TheUncleKai/bbsensor/hardware/RTD/plot/RTD-F_Mask.pdf

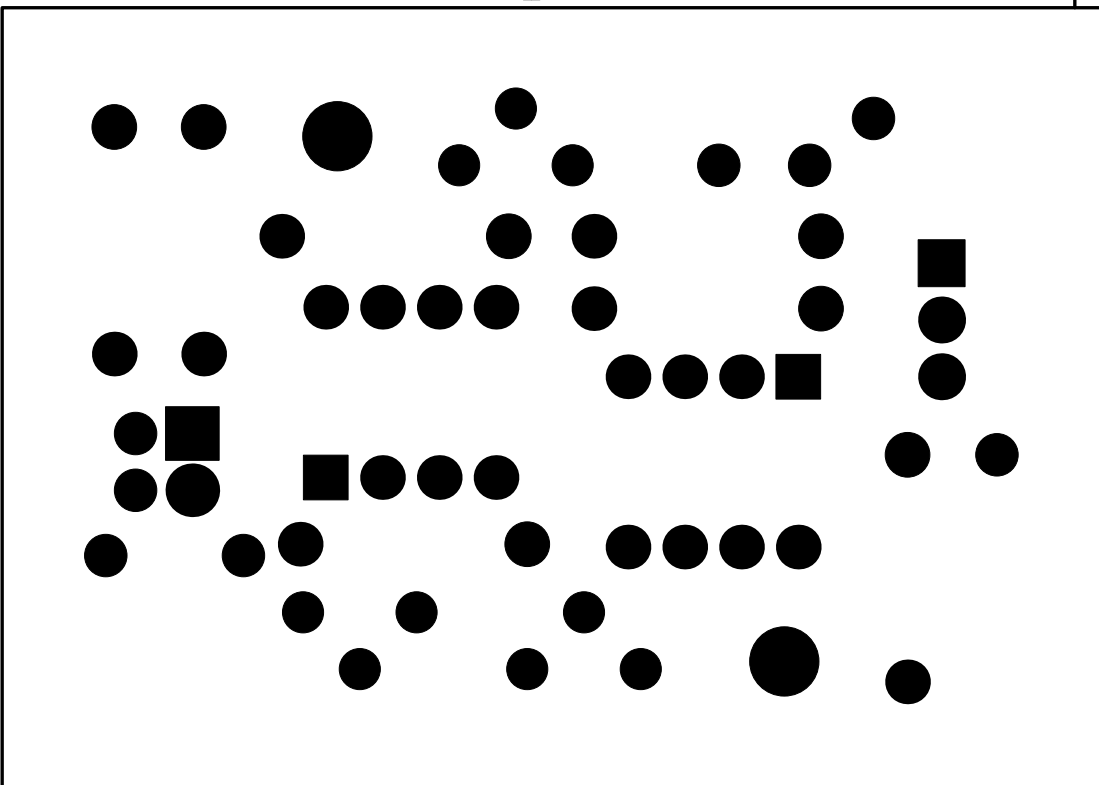
[picture p13: page 1]

File: RTD.kicad_pcb Sheet: Amplifier for Pt100 sensors
