TheUncleKai/bbsensor/hardware/RTD/plot/RTD-F_SilkS.pdf

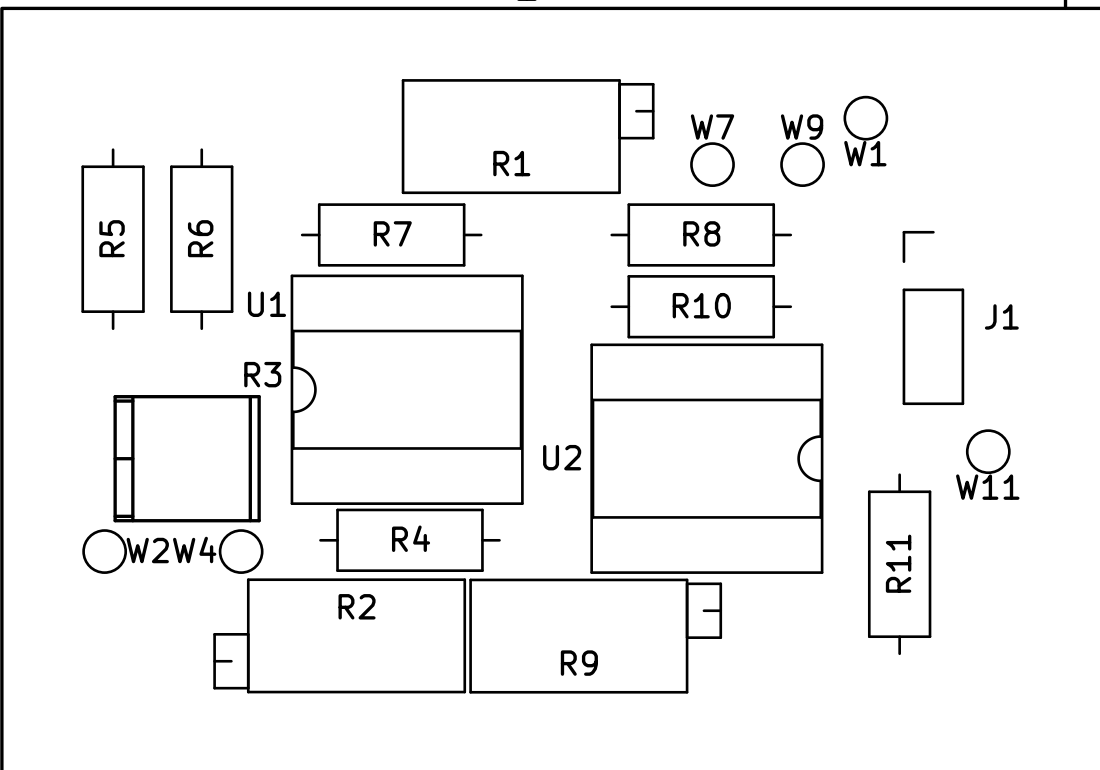
[picture p14: page 1]

File: RTD.kicad_pcb Sheet: Amplifier for Pt100 sensors
