TheUncleKai/bbsensor/hardware/Sensor/plot/BBSensor-B_Cu.pdf

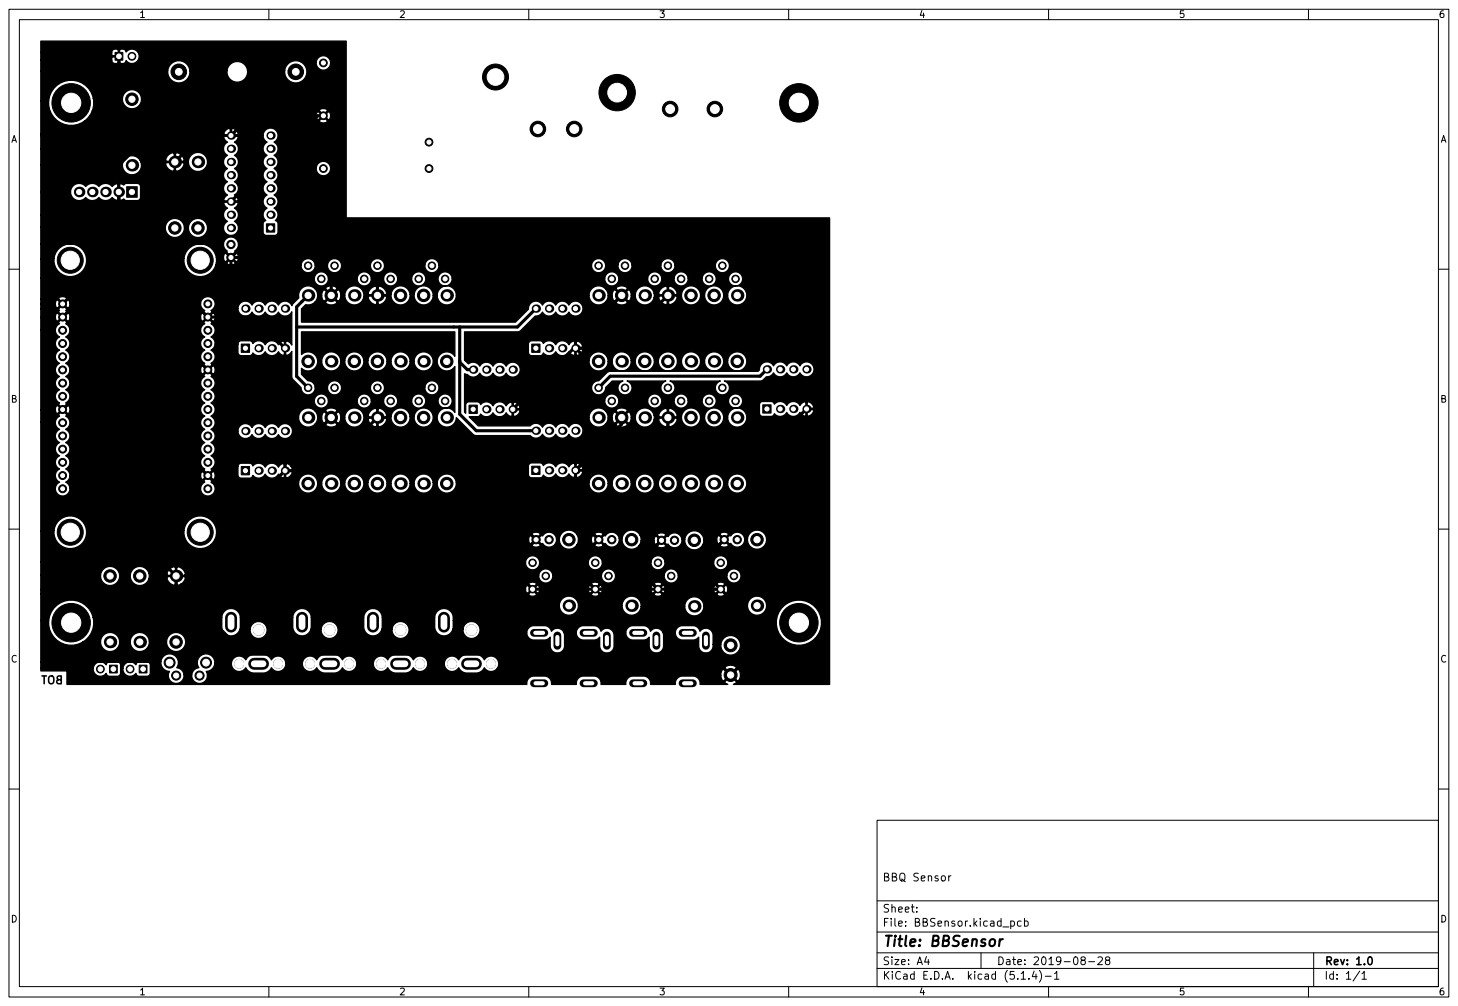
[picture p15: page 1]

File: BBSensor.kicad_pcb Sheet: BBQ Sensor BOT
