TheUncleKai/bbsensor/hardware/Sensor/plot/BBSensor-Edge_Cuts.pdf

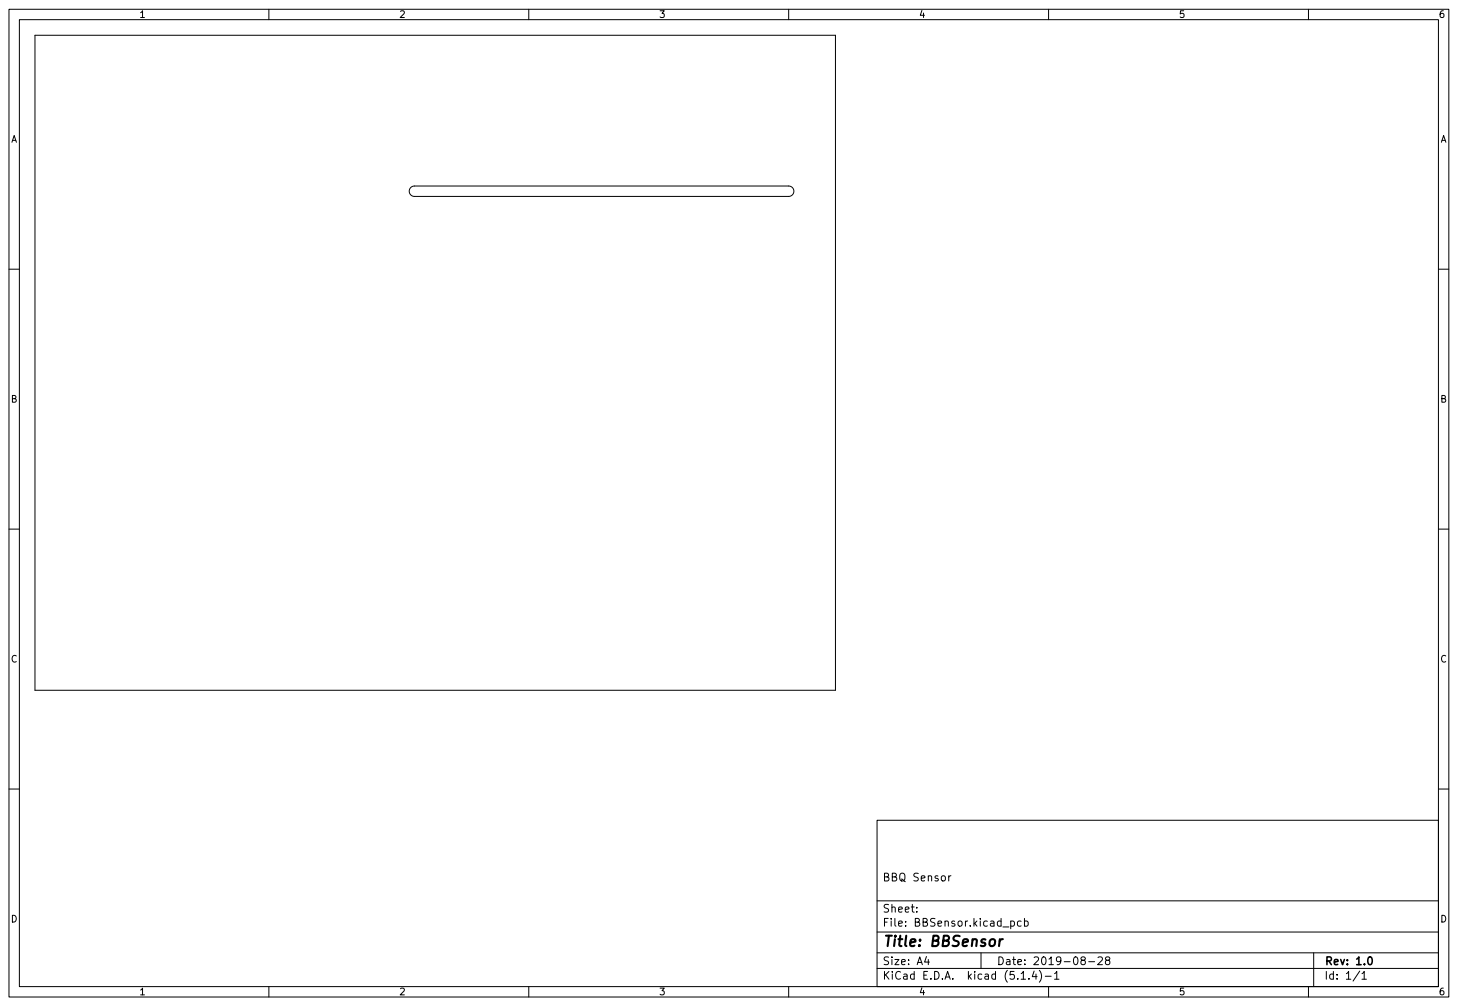
[picture p16: page 1]

File: BBSensor.kicad_pcb Sheet: BBQ Sensor
