TheUncleKai/bbsensor/hardware/Sensor/plot/BBSensor-F_Cu.pdf

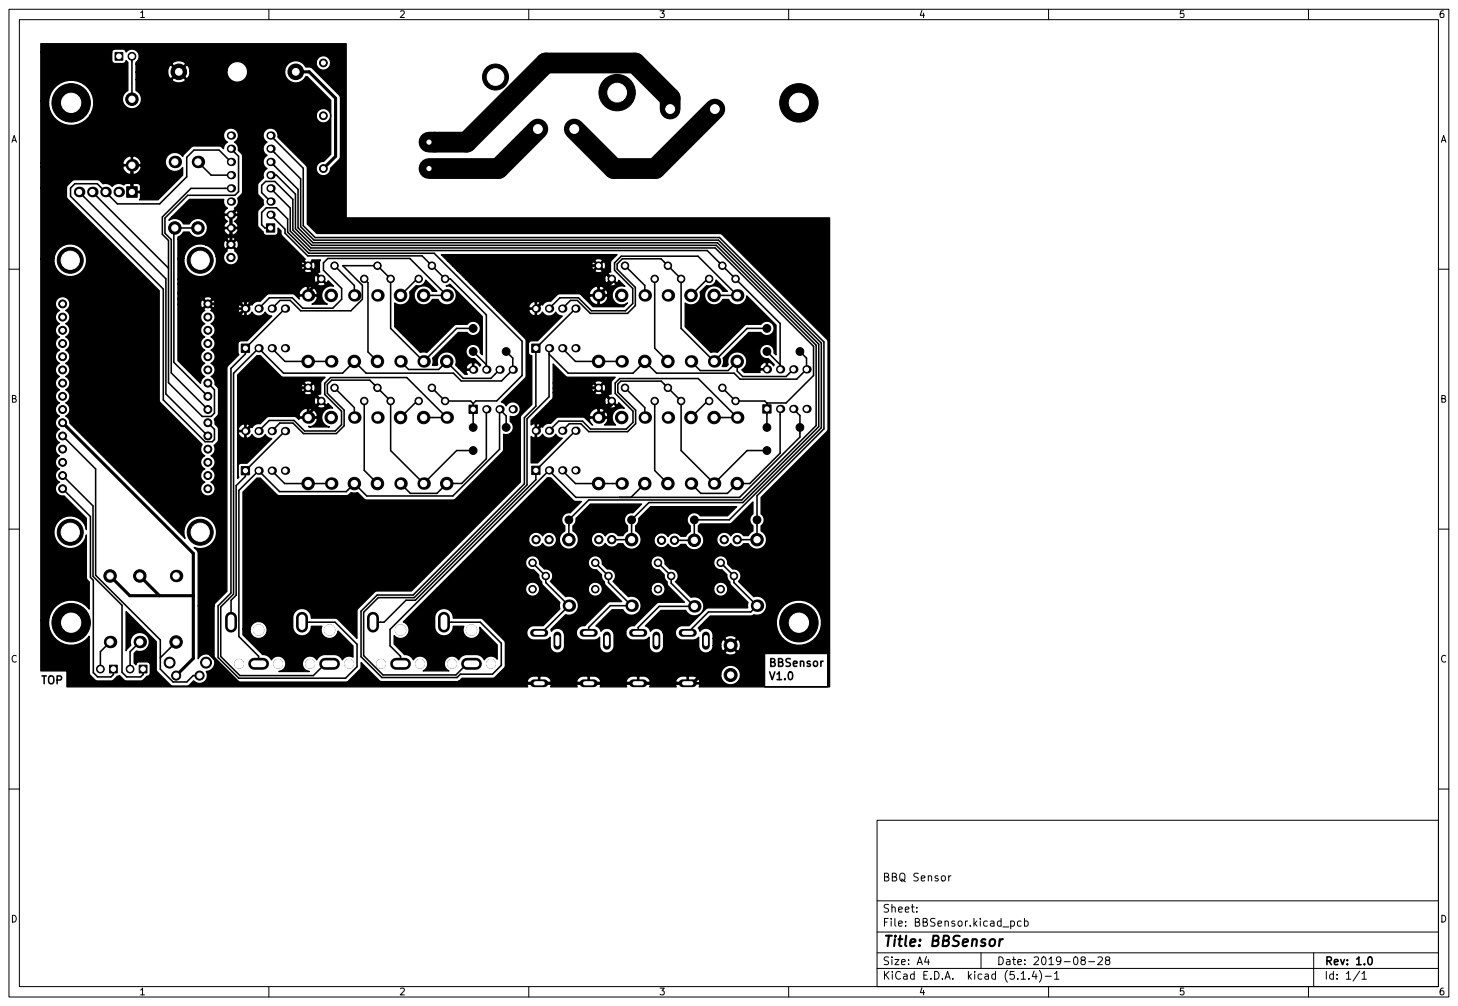
[picture p17: page 1]

File: BBSensor.kicad_pcb Sheet: BBQ Sensor BBSensor V1.0 TOP
