TheUncleKai/bbsensor/doc/pt100.pdf

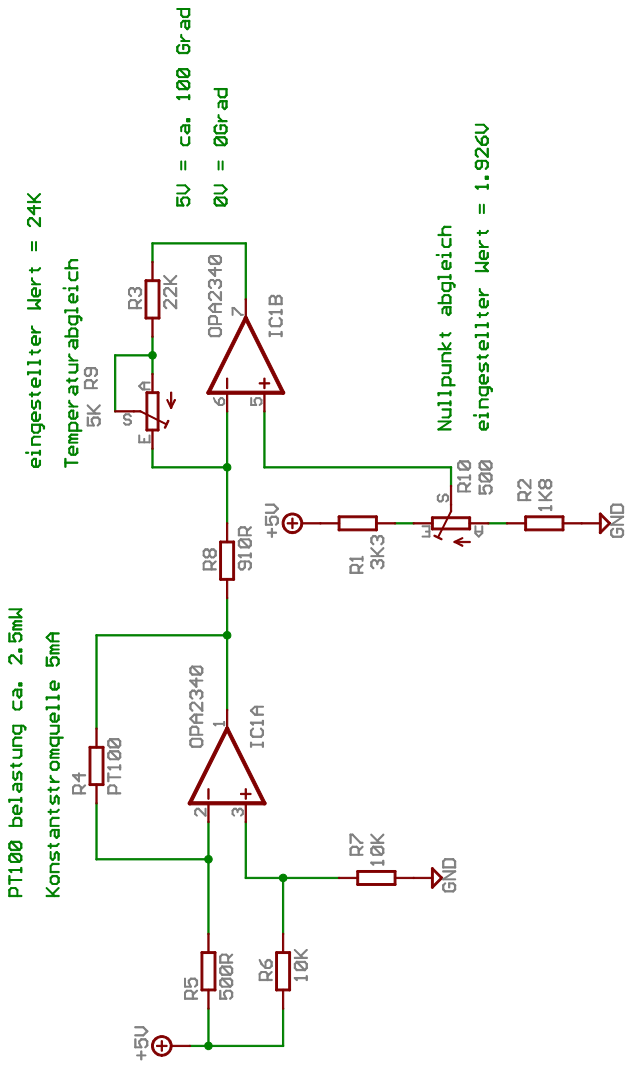
[picture p23: page 1]
