TheUncleKai/bbsensor/doc/pt100_2.pdf

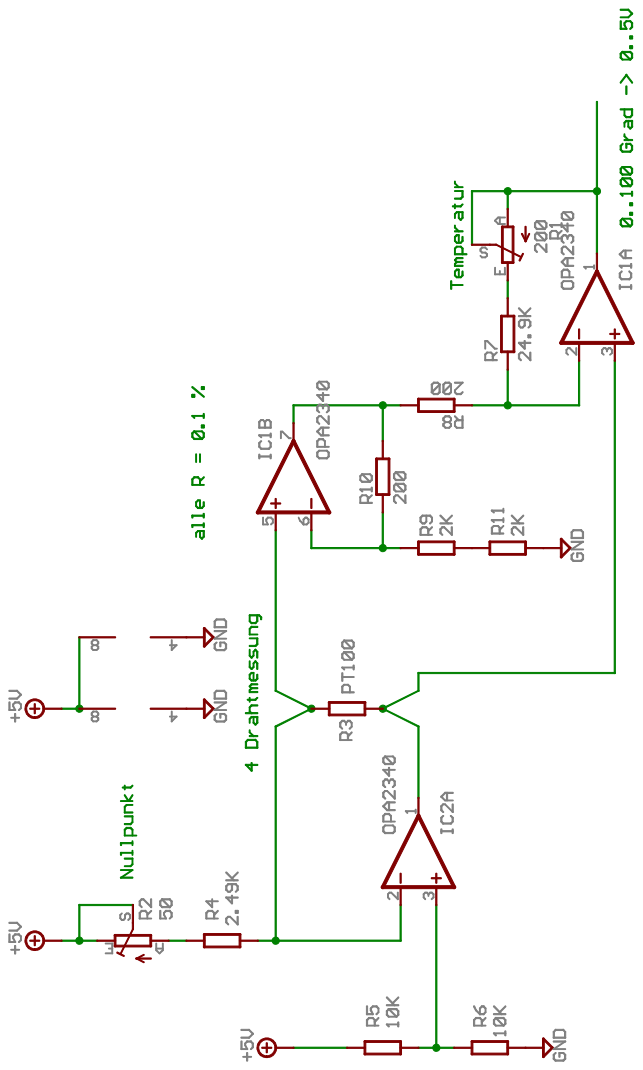
[picture p24: page 1]
