TheUncleKai/bbsensor/doc/pt100_3.pdf

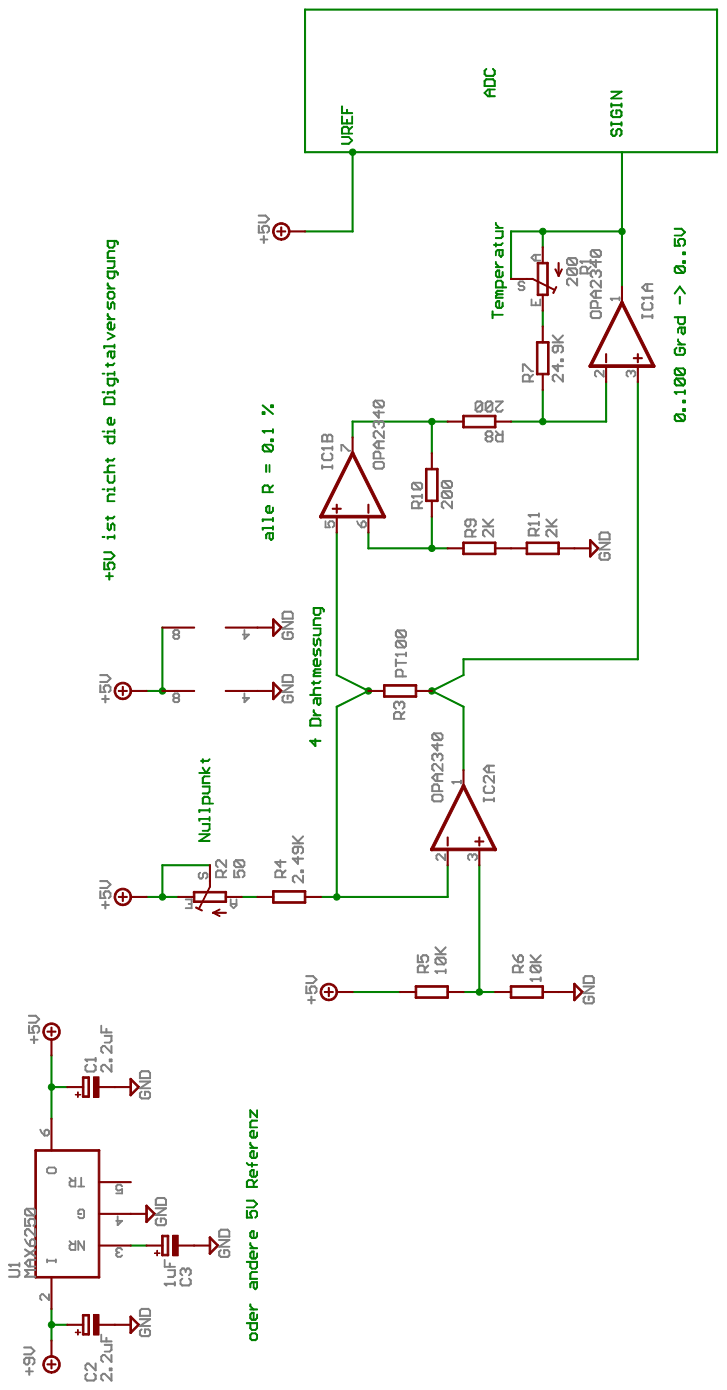
[picture p25: page 1]
