TheUncleKai/bbsensor/doc/pt100_4.pdf

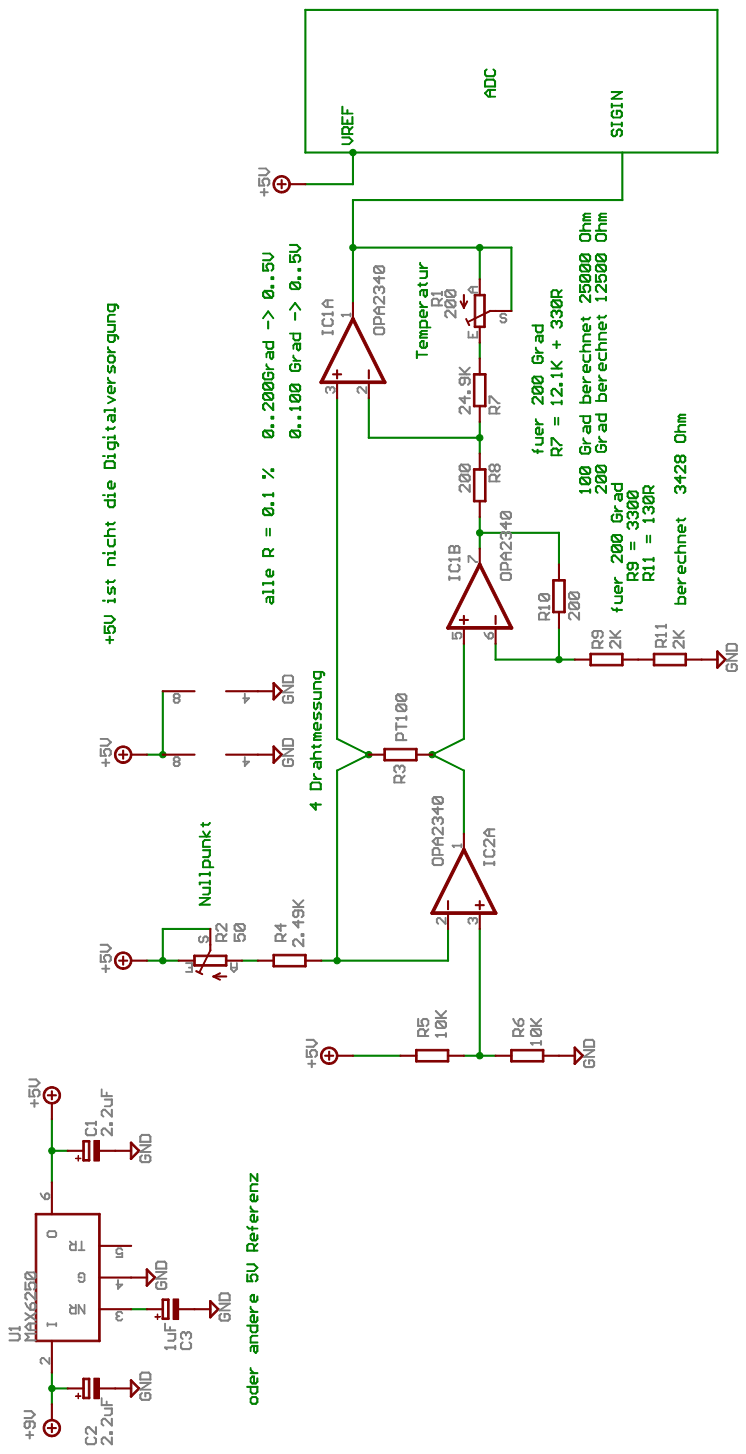
[picture p26: page 1]
