TheUncleKai/bbsensor/doc/pt100_5.pdf

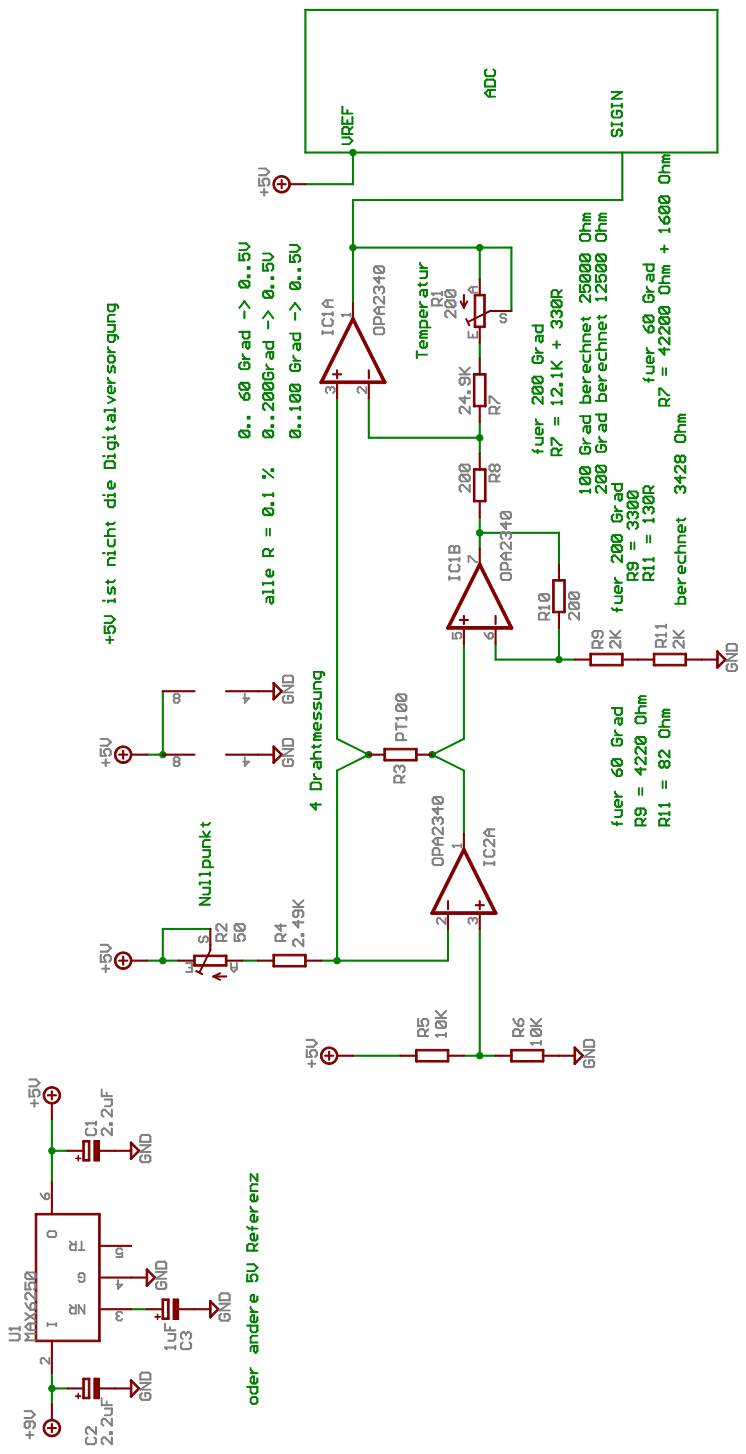
[picture p27: page 1]
