TheUncleKai/bbsensor/doc/pt100_6.pdf

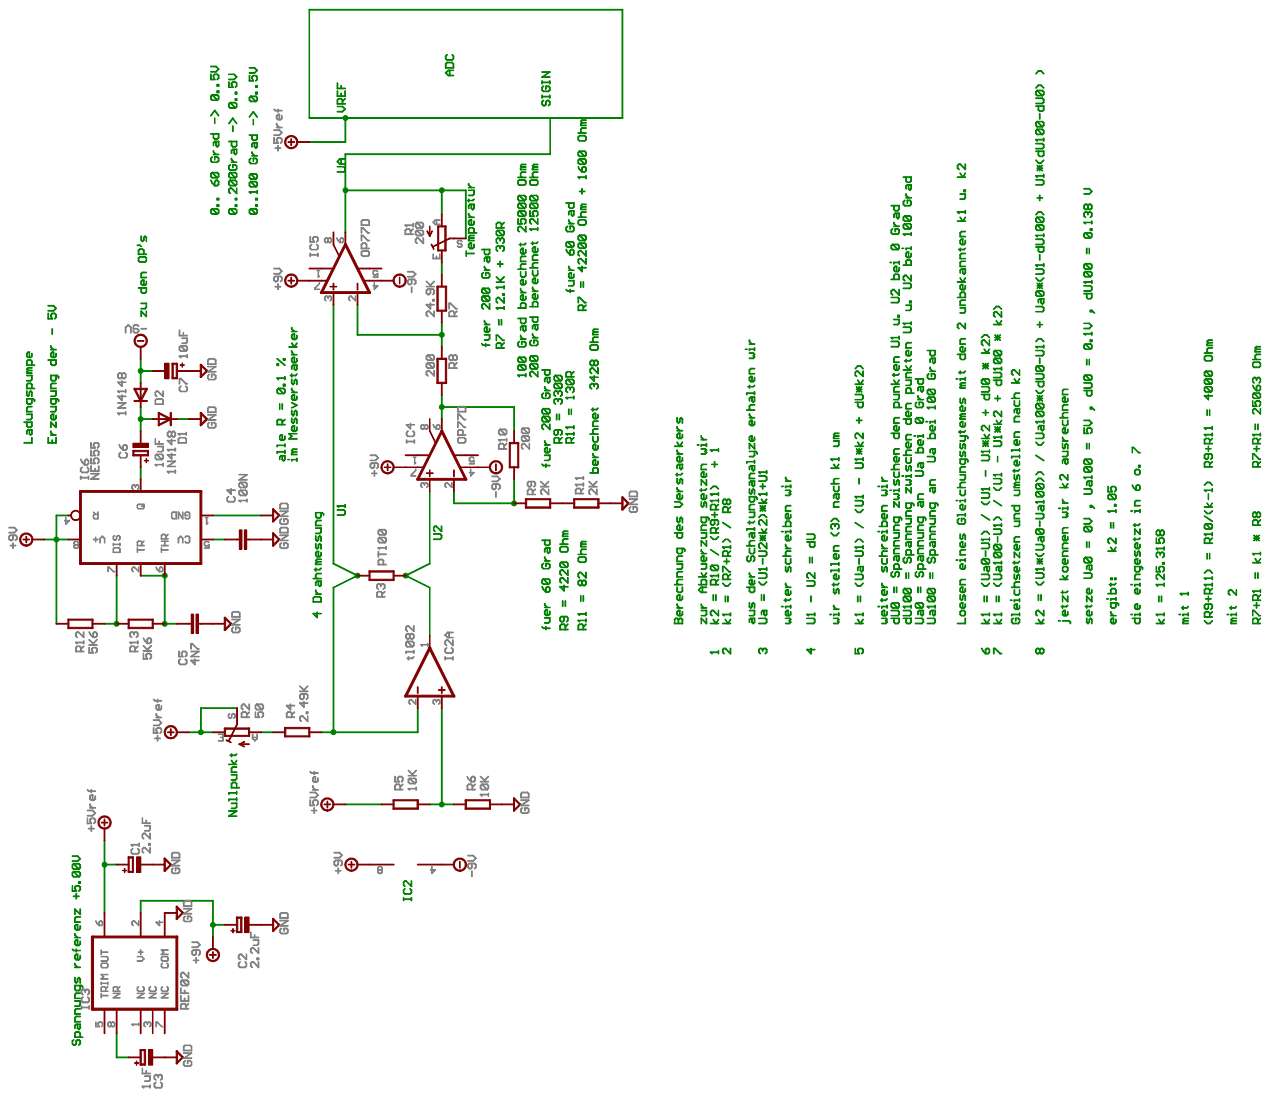
[picture p28: page 1]
