TheUncleKai/bbsensor/doc/pt100_7.pdf

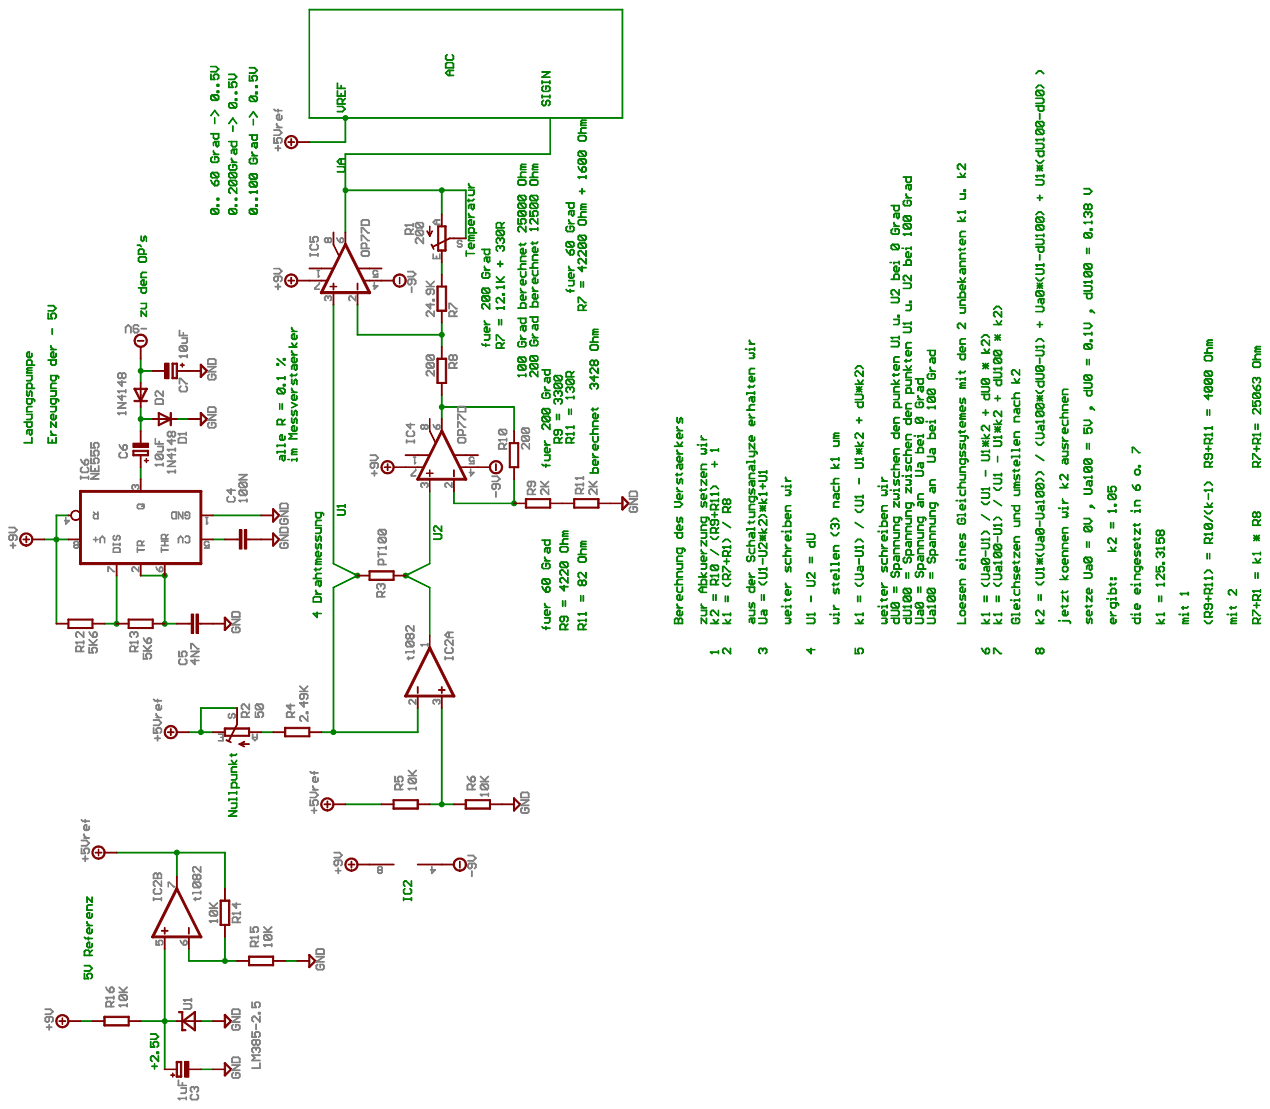
[picture p29: page 1]
