TheUncleKai/bbsensor/hardware/DC/pcb/DC.asc

C1: polcap; 33µ; V=50 Irms=260m Rser=0.6 Lser=0 mfg="Panasonic" pn="ECA1HFQ330" type="Al electrolytic"
C2: cap; 0.1µ; V=25 Irms=1.34 Rser=0.0989014 Lser=0 mfg="KEMET" pn="C0805C104K3RAC" type="X7R"
C3: cap; 0.1µ; V=25 Irms=1.34 Rser=0.0989014 Lser=0 mfg="KEMET" pn="C0805C104K3RAC" type="X7R"
C4: polcap; 33µ; V=50 Irms=260m Rser=0.6 Lser=0 mfg="Panasonic" pn="ECA1HFQ330" type="Al electrolytic"
R1: potentiometer; Rt=500 set=405
R2: potentiometer; Rt=100 set=10
R3: res; 157.33; tol=1 pwr=0.1
R4: res; 2.49K; tol=1 pwr=0.1
R5: res; 10K; tol=1 pwr=0.1
R6: res; 10K; tol=1 pwr=0.1
R7: res; 4700; tol=1 pwr=0.1
R8: res; 200; tol=1 pwr=0.1
R9: res; 390; tol=1 pwr=0.1
R10: res; 200
R11: res; 2K; tol=1 pwr=0.1
R12: res; 100K; tol=1 pwr=0.1
U1: OPA2340
U2: OPA2340
U3: 7805
U4: OPA2340
V1: voltage; 12
Named nets: 0, Vref
.tran 0 1 0 100m
