TheUncleKai/bbsensor/hardware/pcb/ADC.sch

## KiCad design hardware/pcb/ADC.sch (2019-08-30)

Schematic: ADC.sch

Parts:
C201: 100n; C_Disc_D3.4mm_W2.1mm_P2.50mm
U2: MCP3208; DIP-16_W7.62mm_Socket
