TheUncleKai/bbsensor/hardware/pcb/Display.sch

## KiCad design hardware/pcb/Display.sch (2019-08-30)

Schematic: Display.sch

Parts:
C301: 100n; C_Disc_D3.4mm_W2.1mm_P2.50mm
R301: 220; R_Axial_DIN0411_L9.9mm_D3.6mm_P12.70mm_Horizontal
R302: 2k; R_Axial_DIN0411_L9.9mm_D3.6mm_P12.70mm_Horizontal
U3: 74HC595; DIP-16_W7.62mm_Socket
U4: HD44780; Box_Header_Straight_2x08
