TheUncleKai/bbsensor/hardware/pcb/ESP8266.sch

## KiCad design hardware/pcb/ESP8266.sch (2019-08-30)

Schematic: ESP8266.sch

Parts:
D101: RED; 5600F
D102: GREEN; 5600F
R101: 1k; R_Axial_DIN0411_L9.9mm_D3.6mm_P12.70mm_Horizontal
R102, R153: 2k2; R_Axial_DIN0411_L9.9mm_D3.6mm_P12.70mm_Horizontal
R150, R151: 140; R_Axial_DIN0411_L9.9mm_D3.6mm_P12.70mm_Horizontal
SW1: SW_Push; SW_Tactile_SPST_Angled_PTS645Vx83-2LFS
U1: ESP8266-12E_NodeMCU_Lolin

Notes on the sheet:
CS2
MOSI
CS1
MISO
SCLK
