TheUncleKai/bbsensor/hardware/pcb/Power.sch

## KiCad design hardware/pcb/Power.sch (2019-08-30)

Schematic: Power.sch

Parts:
D1: POWER; 5600F
F1: Fuse; Fuse_holder_20x5_22.5
J1: Earth; Terminal_Pin_D1.3_L10.0_PL4.0
P1: Conn_WallPlug_Earth; PX0580PC
PS1: TMPS_05; Traco_TMPS_05
R1: 220; R_Axial_DIN0411_L9.9mm_D3.6mm_P12.70mm_Horizontal
TP1, TP2: TestPoint; TestPoint_THTPad_D2.5mm_Drill1.2mm
