TheUncleKai/bbsensor/hardware/pcb/Temperature1.sch

## KiCad design hardware/pcb/Temperature1.sch (2019-08-30)

Schematic: Temperature1.sch

Parts:
R4004, R4104: 2k2; R_Axial_DIN0411_L9.9mm_D3.6mm_P12.70mm_Horizontal
R4005, R4006, R4105, R4106: 10k; R_Axial_DIN0411_L9.9mm_D3.6mm_P12.70mm_Horizontal
R4007, R4107: 4k7; R_Axial_DIN0411_L9.9mm_D3.6mm_P12.70mm_Horizontal
R4008, R4010, R4108, R4110: 200; R_Axial_DIN0411_L9.9mm_D3.6mm_P12.70mm_Horizontal
R4011, R4111: 2k; R_Axial_DIN0411_L9.9mm_D3.6mm_P12.70mm_Horizontal
RV4001, RV4101: 405; Potentiometer_Bourns_3296Y_Vertical
RV4002, RV4102: 300; Potentiometer_Bourns_3296Y_Vertical
RV4009, RV4109: 470; Potentiometer_Bourns_3296Y_Vertical
TH1, TH2: Thermistor_NTC; LUMBERG_1553_02
TP4001, TP4004, TP4009, TP4101, TP4104, TP4109: TestPoint; TestPoint_Pad_D1.5mm
U100, U101, U110: OPA2340; DIP-8_W7.62mm_Socket
