TheUncleKai/bbsensor/hardware/pcb/Temperature2.sch

## KiCad design hardware/pcb/Temperature2.sch (2019-08-30)

Schematic: Temperature2.sch

Parts:
R4204, R4304: 2k2; R_Axial_DIN0411_L9.9mm_D3.6mm_P12.70mm_Horizontal
R4205, R4206, R4305, R4306: 10k; R_Axial_DIN0411_L9.9mm_D3.6mm_P12.70mm_Horizontal
R4207, R4307: 4k7; R_Axial_DIN0411_L9.9mm_D3.6mm_P12.70mm_Horizontal
R4208, R4210, R4308, R4310: 200; R_Axial_DIN0411_L9.9mm_D3.6mm_P12.70mm_Horizontal
R4211, R4311: 2k; R_Axial_DIN0411_L9.9mm_D3.6mm_P12.70mm_Horizontal
RV4201, RV4301: 405; Potentiometer_Bourns_3296Y_Vertical
RV4202, RV4302: 300; Potentiometer_Bourns_3296Y_Vertical
RV4209, RV4309: 470; Potentiometer_Bourns_3296Y_Vertical
TH3, TH4: Thermistor_NTC; LUMBERG_1553_02
TP4201, TP4204, TP4209, TP4301, TP4304, TP4309: TestPoint; TestPoint_Pad_D1.5mm
U102, U103, U120: OPA2340; DIP-8_W7.62mm_Socket
