TheUncleKai/bbsensor/hardware/pcb/Temperature3.sch

## KiCad design hardware/pcb/Temperature3.sch (2019-08-30)

Schematic: Temperature3.sch

Parts:
C501, C502, C503, C504: 100n; C_Disc_D3.4mm_W2.1mm_P2.50mm
J501, J502, J503, J504: AudioJack2_SwitchT; LUMBERG_1501_09
R501, R502, R503, R504: 10k; R_Axial_DIN0411_L9.9mm_D3.6mm_P12.70mm_Horizontal
RV501, RV502, RV503, RV504: 10k; Potentiometer_Bourns_3296Y_Vertical
TP501, TP502, TP503, TP504: TestPoint; TestPoint_Pad_D1.5mm
