TheUncleKai/bbsensor/firmware/app/tables.cpp

/*
   Copyright (C) 2019, Kai Raphahn

   Licensed under the Apache License, Version 2.0 (the "License");
   you may not use this file except in compliance with the License.
   You may obtain a copy of the License at

       http://www.apache.org/licenses/LICENSE-2.0

   Unless required by applicable law or agreed to in writing, software
   distributed under the License is distributed on an "AS IS" BASIS,
   WITHOUT WARRANTIES OR CONDITIONS OF ANY KIND, either express or implied.
   See the License for the specific language governing permissions and
   limitations under the License.
*/

#include <tables.h>

const float table_voltages[4096] = {
    0,
    0.001,
    0.002,
    0.004,
    0.005,
    0.006,
    0.007,
    0.009,
    0.010,
    0.011,
    0.012,
    0.013,
    0.015,
    0.016,
    0.017,
    0.018,
    0.020,
    0.021,
    0.022,
    0.023,
    0.024,
    0.026,
    0.027,
    0.028,
    0.029,
    0.031,
    0.032,
    0.033,
    0.034,
    0.035,
    0.037,
    0.038,
    0.039,
    0.040,
    0.042,
    0.043,
    0.044,
    0.045,
    0.046,
    0.048,
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
};


const float table_rtd[4096] = {
    0,
    0.001,
    0.002,
    0.004,
    0.005,
    0.006,
    0.007,
    0.009,
    0.010,
    0.011,
    0.012,
    0.013,
    0.015,
    0.016,
    0.017,
    0.018,
    0.020,
    0.021,
    0.022,
    0.023,
    0.024,
    0.026,
    0.027,
    0.028,
    0.029,
    0.031,
    0.032,
    0.033,
    0.034,
    0.035,
    0.037,
    0.038,
    0.039,
    0.040,
    0.042,
    0.043,
    0.044,
    0.045,
    0.046,
    0.048,
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
};


const float table_ptc10[4096] = {
    0,
    0.001,
    0.002,
    0.004,
    0.005,
    0.006,
    0.007,
    0.009,
    0.010,
    0.011,
    0.012,
    0.013,
    0.015,
    0.016,
    0.017,
    0.018,
    0.020,
    0.021,
    0.022,
    0.023,
    0.024,
    0.026,
    0.027,
    0.028,
    0.029,
    0.031,
    0.032,
    0.033,
    0.034,
    0.035,
    0.037,
    0.038,
    0.039,
    0.040,
    0.042,
    0.043,
    0.044,
    0.045,
    0.046,
    0.048,
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
};


const float table_ptc100[4096] = {
    0,
    0.001,
    0.002,
    0.004,
    0.005,
    0.006,
    0.007,
    0.009,
    0.010,
    0.011,
    0.012,
    0.013,
    0.015,
    0.016,
    0.017,
    0.018,
    0.020,
    0.021,
    0.022,
    0.023,
    0.024,
    0.026,
    0.027,
    0.028,
    0.029,
    0.031,
    0.032,
    0.033,
    0.034,
    0.035,
    0.037,
    0.038,
    0.039,
    0.040,
    0.042,
    0.043,
    0.044,
    0.045,
    0.046,
    0.048,
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
};
